yenthusiastic/Musical-Wristband/Media/Photo 5.3.jpg

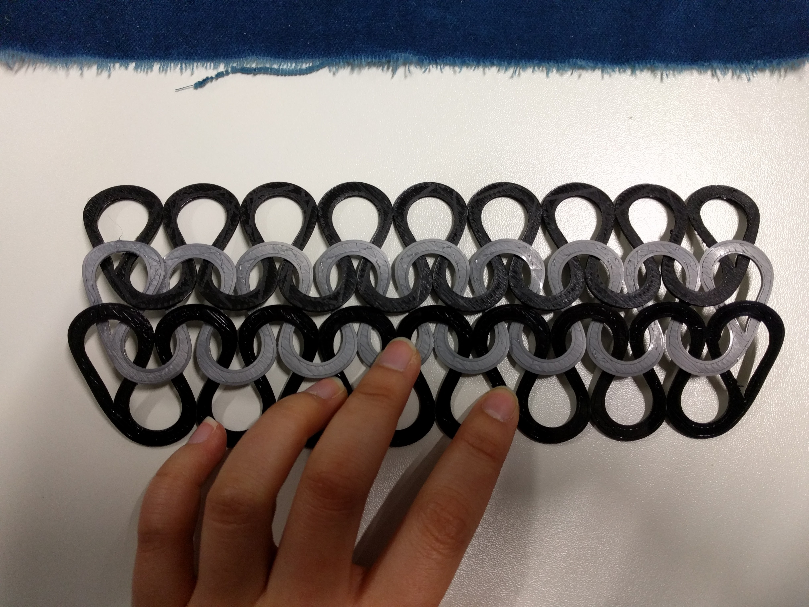
Media/Photo 5.3.jpg
