yenthusiastic/Musical-Wristband/Media/Photo 5.7.jpg

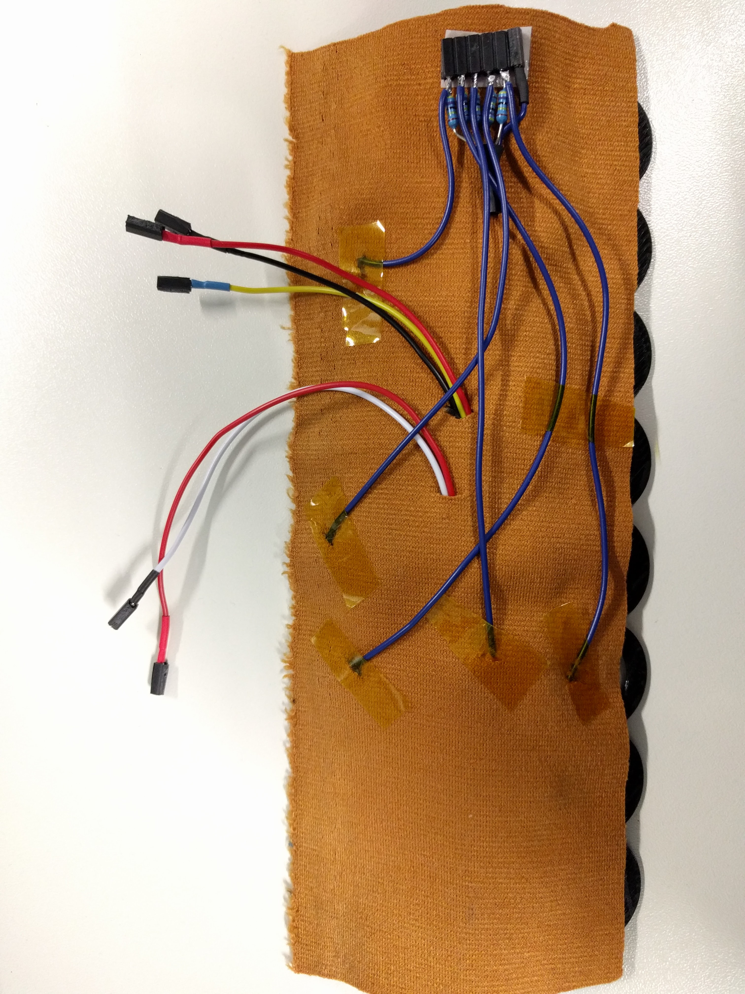
Media/Photo 5.7.jpg
